ideocentric/ribbon-synth/hardware/pcb/absonus-v0.2/hook up/IMG_1598.jpeg

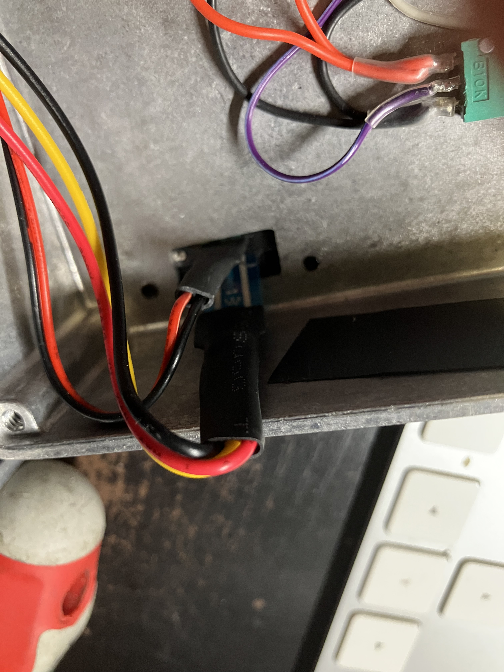
hardware/pcb/absonus-v0.2/hook up/IMG_1598.jpeg
