ideocentric/ribbon-synth/hardware/enclosure/enclosure-v2.dxf

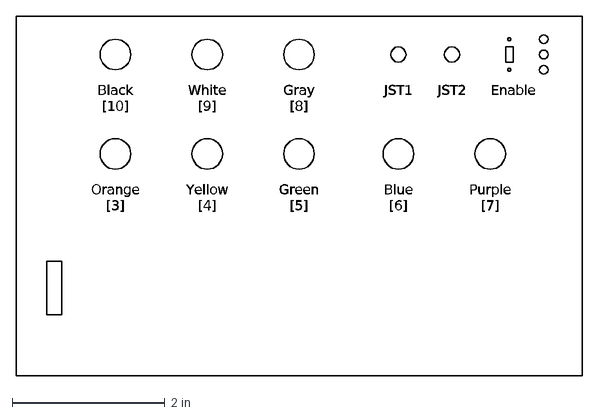
[picture p25: CAD file, 2026-04-06]
hardware/enclosure/enclosure-v2.dxf
Enable
JST2
JST1
Gray [8]
White [9]
Black [10]
Purple [7]
Blue [6]
Green [5]
Yellow [4]
Orange [3]
