ideocentric/ribbon-synth/hardware/pcb/absonus-v0.2/hook up/IMG_1602.jpeg

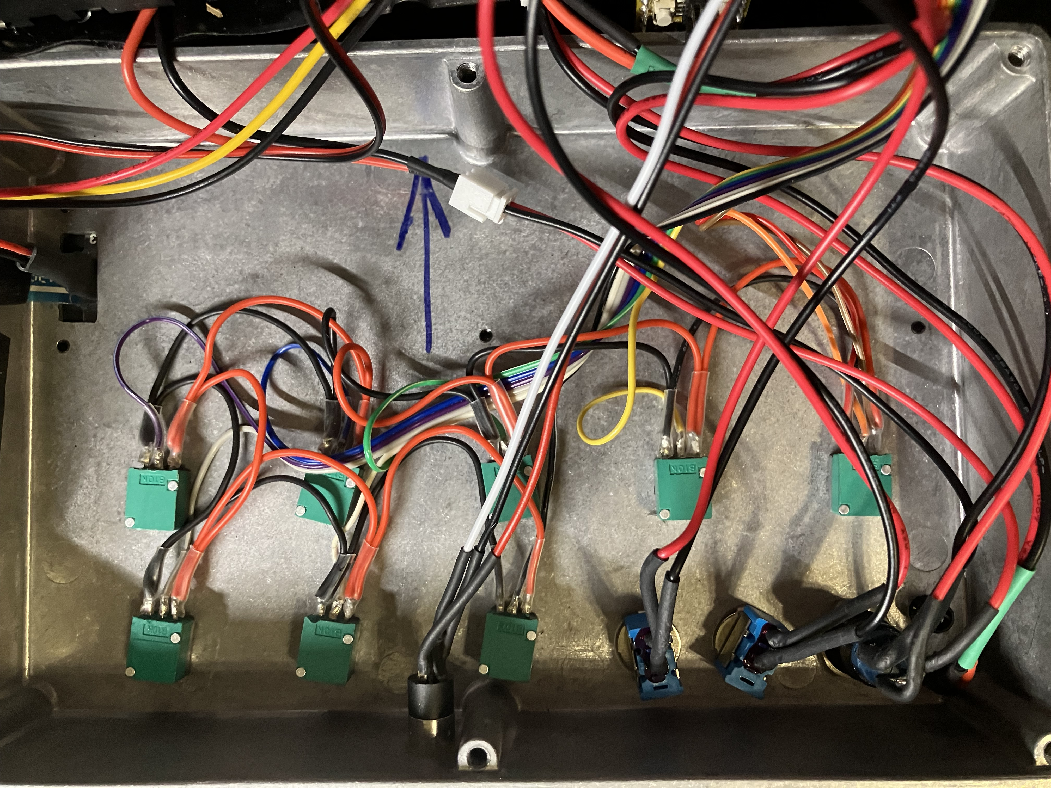
hardware/pcb/absonus-v0.2/hook up/IMG_1602.jpeg
